axtar/14-digits-nixie-calculator/Docs/!_Start here.pdf

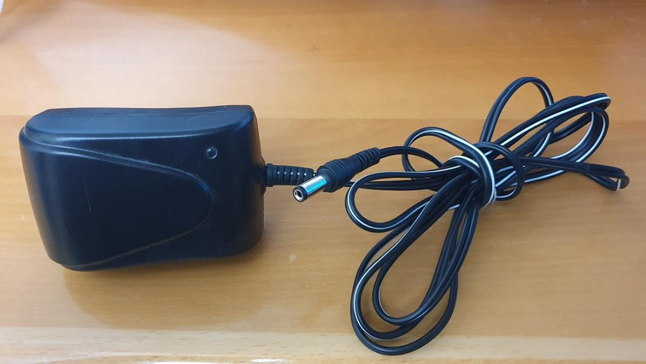
[picture p9: figure]
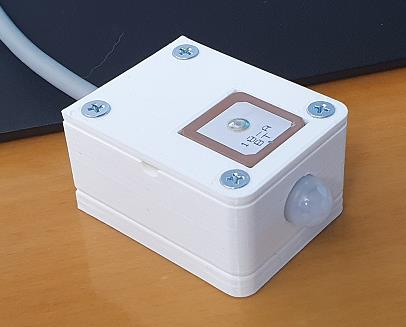
[picture p10: figure]
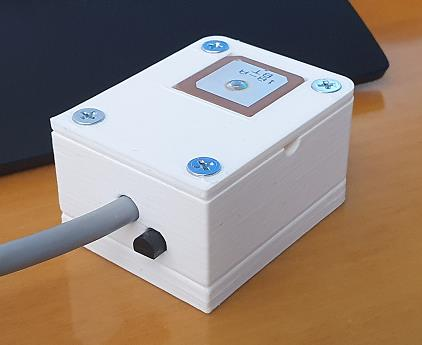
[picture p11: figure]

June 16, 2021 | Start here – Version 0.1 | Page 1 of 1

## Start here

### WARNING: nixies need high voltage to light up. If you choose to build the

calculator, you are doing so at your own risk.

Please read all the documents in Docs first.

### BOM/Components

I have tried to use available and modern components but currently some of the IC’s have long lead times. That seems to be a common problem these days.

### Power supply

The calculator needs a stabilized 12V DC 2A center positive power supply.

### Optional peripherals

You can connect a GPS module with U-Blox chip, a PIR and a DS18B20+ temperature sensor. All the peripherals must work with 5V input voltage and 3.3V logic. The pictures show the all-in-one solution I designed for this project.
