axtar/14-digits-nixie-calculator/Docs/Importing PCB project files.pdf

June 10, 2021 | Draft – Version 0.1 | Page 1 of 1

## Importing PCB project files

I will not provide the Gerber files, but you can import the project files into EasyEDA. This way, you can check the design and modify the boards according to your needs. You generate your own Gerber files, and it is up to you to make sure that they are correct.

To import the projects, try this or follow the instructions on EasyEDA:

- Unzip the project file, you will get a schematic and a pcb file (json format)

Go to EasyEDA Designer (you need an account)

- Import schematic

->File->Open->EasyEDA

Select schematic file

->Open

- Save schematic:

->File->Save As

Select -Save as New Project-

Enter -Title- (a different name for every project you want to import)

->Save

- Import PCB:

->File->Open->EasyEDA

Select PCB file

->Open

- Save pcb:

->File->Save As

Select -Save to Existing Project-

Enter -Title- (board name)

Set the -Project Owner- to yourself

Select -Project- (the project you created before)

->Save

The label board has no schematic, you can import just the PCB file and save it as new project.
