axtar/14-digits-nixie-calculator/Docs/Keyboard layout.pdf

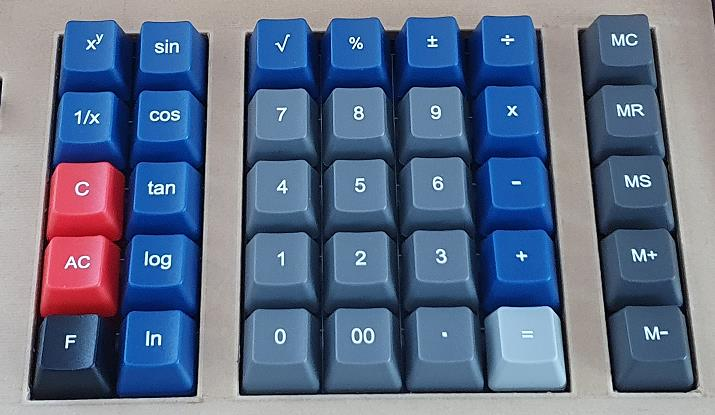
[picture p12: figure]

June 11, 2021 | Draft - Version 0.1 | Page 1 of 2

## Keyboard layout

For this project we need some custom Cherry MX keycaps. The picture shows the keyboard layout and the keycap type (Row1 – Row4). All keycaps are 1x1.

R4 →
R3 →
R2 →
R1 →
R1 →

Classic

You can order some blank keycaps and print your own legends, for example using sublimation ink, sublimation paper and an inkjet printer. You can also order custom keycaps from a service provider.

I’ve used Inkscape to modify the 104-key template file (V6.0) provided by WASD Keyboards. I cannot provide the template file but in the svg file you can see the legends layer I have designed for my keyboard.

If you decide to use my design as a starting point, you can try this:

- Download the 104-key template file for Inkscape from the support area
- Open the template with Inkscape and hide the “message” layer
- Add a new layer called “Nixie Calculator” and make sure it’s selected, visible and unlocked
- Open another instance of Inkscape
- Open the “Keycaps/Nixie_Calculator_extended.svg” file
- Select all legends (ctrl-a). Make a note of the X and Y coordinates of the selection
- Copy the legends (ctrl-c)
- Go to the instance with the template file
- Paste the legends (ctrl-v)
- Bring the legends into position by setting the X and Y coordinates to the previously noted values. Now you can modify the legends as you wish. Check that everything is correctly aligned.
- Important: set the desired legend colors. If you want white legends as shown in the picture, you must set the text color to white.
- Unhide the “message” layer and carefully read and follow the instructions shown in the template before placing your order.

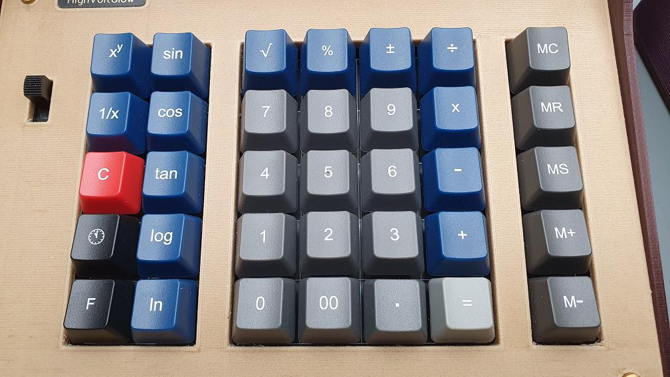
[picture p13: figure]

June 11, 2021 | Draft - Version 0.1 | Page 2 of 2

I can think of two options:

- Classic mode:
F | -> clock mode and settings
AC | -> all clear
C | -> clear last
- Alternate mode:
F -> shift (second level of functions)
- -> clock mode and settings
C -> all clear

Alternate

If you want to use the alternate mode, it is also possible to add a second level of functions to the keycap legends. For example, something like this:
