axtar/14-digits-nixie-calculator/PCB/Pictures/Boards 2D/Nixie Calculator Extended Keyboard Bottom 2D.jpg

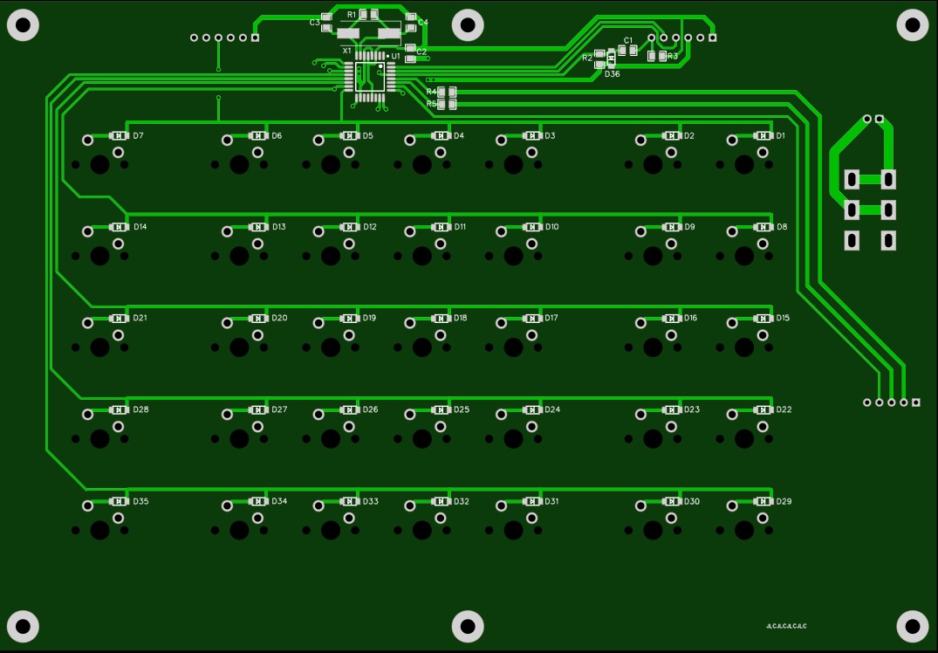
PCB/Pictures/Boards 2D/Nixie Calculator Extended Keyboard Bottom 2D.jpg
