axtar/14-digits-nixie-calculator/PCB/Pictures/Boards 2D/Nixie Calculator IN-16 Display With Sockets Bottom 2D.jpg

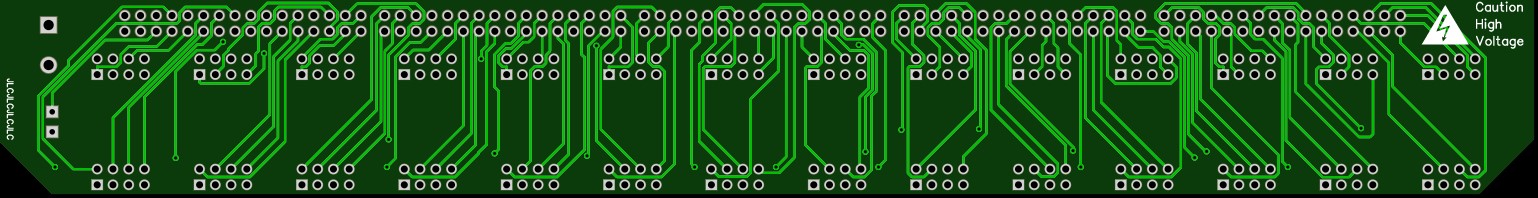
PCB/Pictures/Boards 2D/Nixie Calculator IN-16 Display With Sockets Bottom 2D.jpg
