axtar/14-digits-nixie-calculator/PCB/Pictures/Boards 2D/Nixie Calculator IN-16 Driver Top 2D.jpg

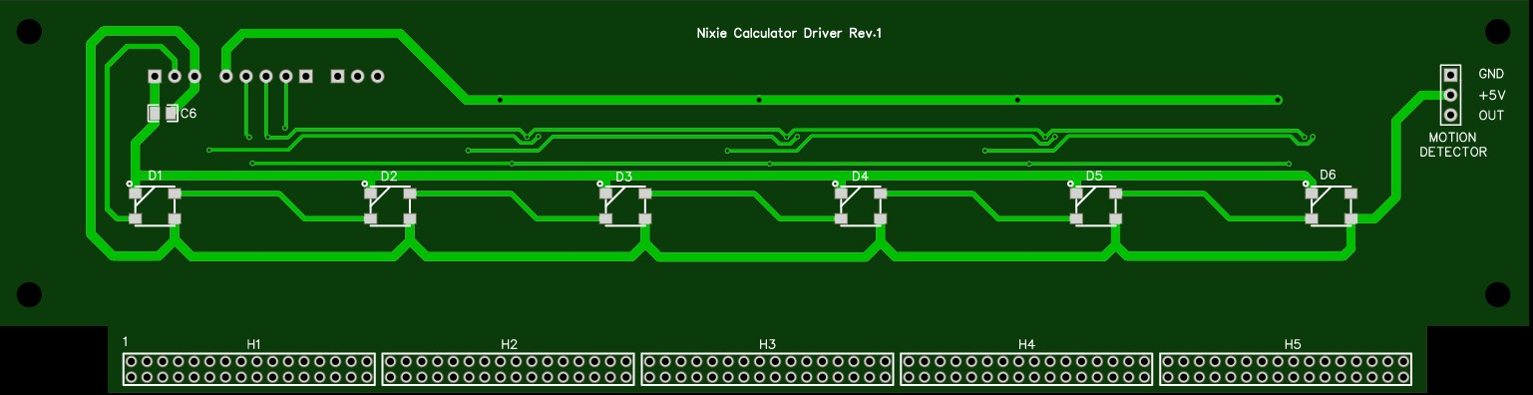
PCB/Pictures/Boards 2D/Nixie Calculator IN-16 Driver Top 2D.jpg
