axtar/14-digits-nixie-calculator/PCB/Pictures/Boards 2D/Nixie Calculator IN-17 Display & Driver With Sockets Top 2D.jpg

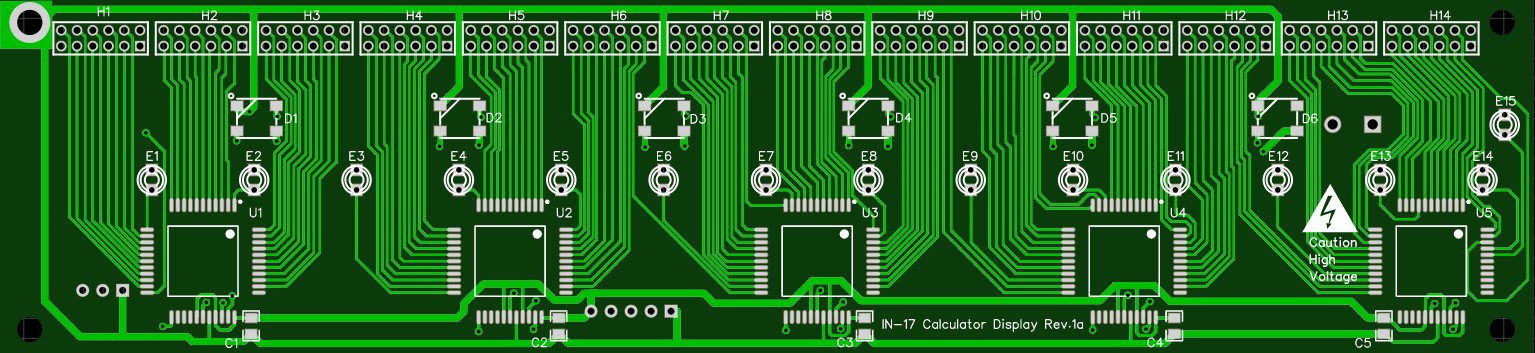
PCB/Pictures/Boards 2D/Nixie Calculator IN-17 Display & Driver With Sockets Top 2D.jpg
