axtar/14-digits-nixie-calculator/PCB/Pictures/Boards 2D/Nixie Calculator IN-17 Socket Top 2D.jpg

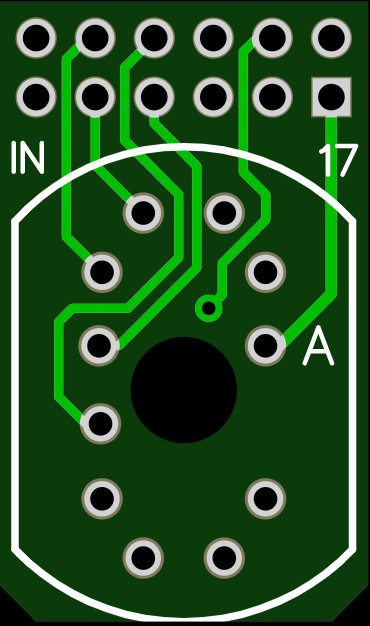
PCB/Pictures/Boards 2D/Nixie Calculator IN-17 Socket Top 2D.jpg
