axtar/14-digits-nixie-calculator/PCB/Pictures/Boards 3D/Nixie  Calculator Controller Top 3D.jpg

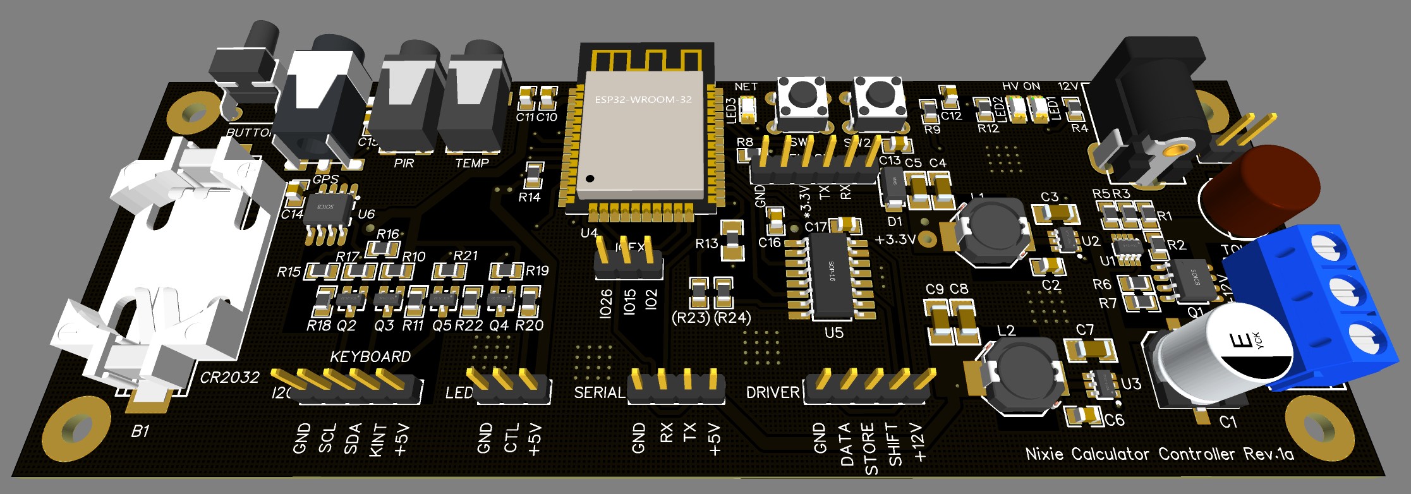
PCB/Pictures/Boards 3D/Nixie Calculator Controller Top 3D.jpg
