axtar/14-digits-nixie-calculator/PCB/Pictures/Boards 3D/Nixie Calculator Extended Keyboard Top  3D.jpg

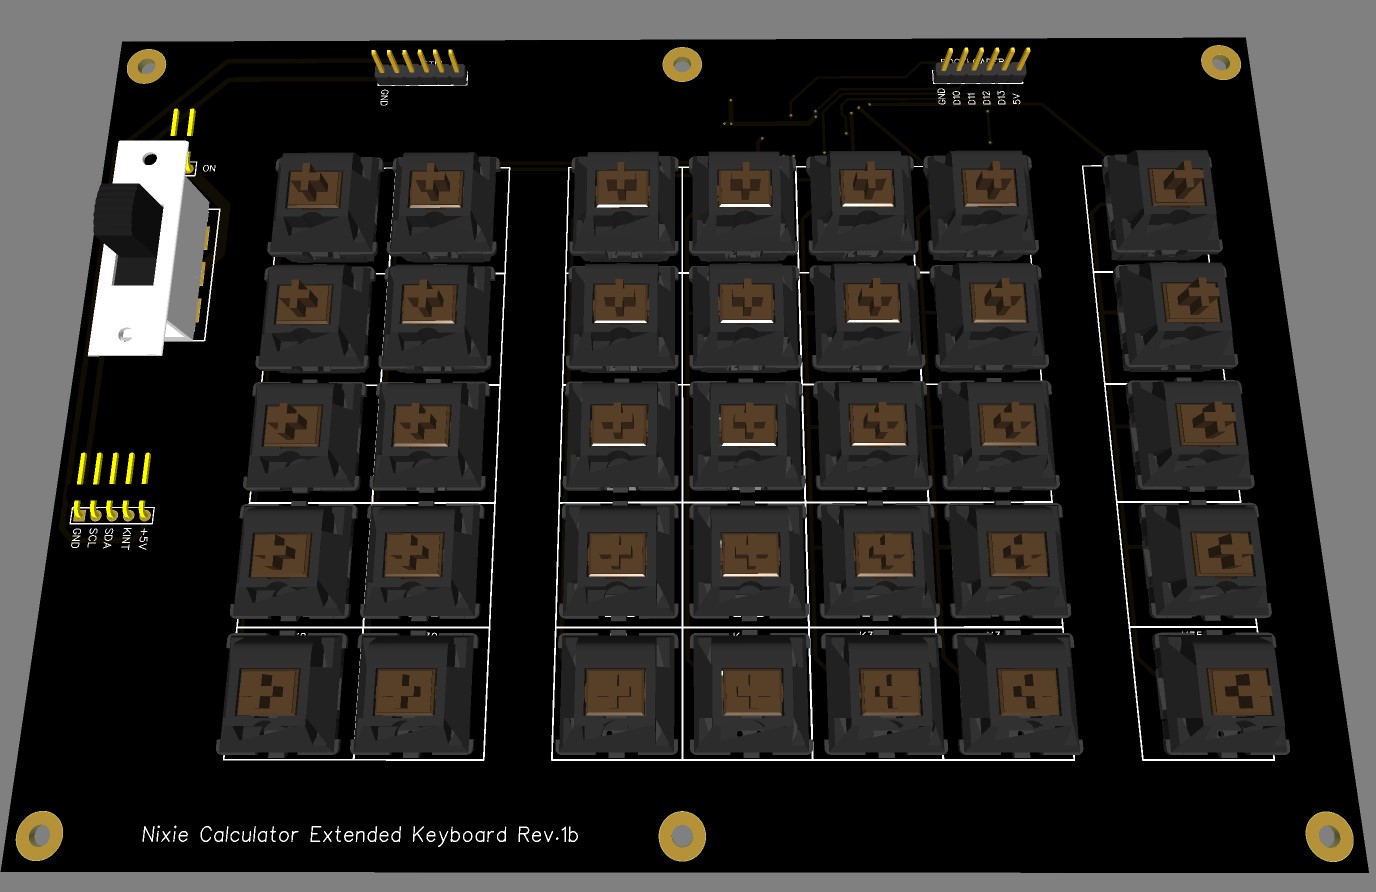
PCB/Pictures/Boards 3D/Nixie Calculator Extended Keyboard Top 3D.jpg
