axtar/14-digits-nixie-calculator/PCB/Pictures/Boards 3D/Nixie Calculator High Voltage PSU Top 3D.jpg

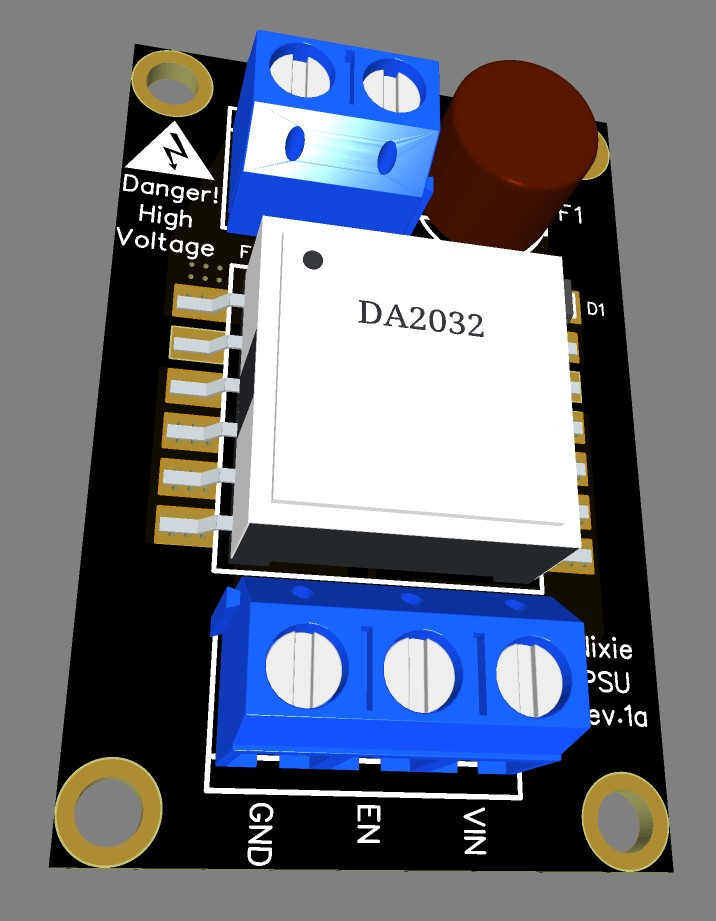
PCB/Pictures/Boards 3D/Nixie Calculator High Voltage PSU Top 3D.jpg
