axtar/14-digits-nixie-calculator/PCB/Pictures/Boards 3D/Nixie Calculator IN-16 Driver Top 3D.jpg

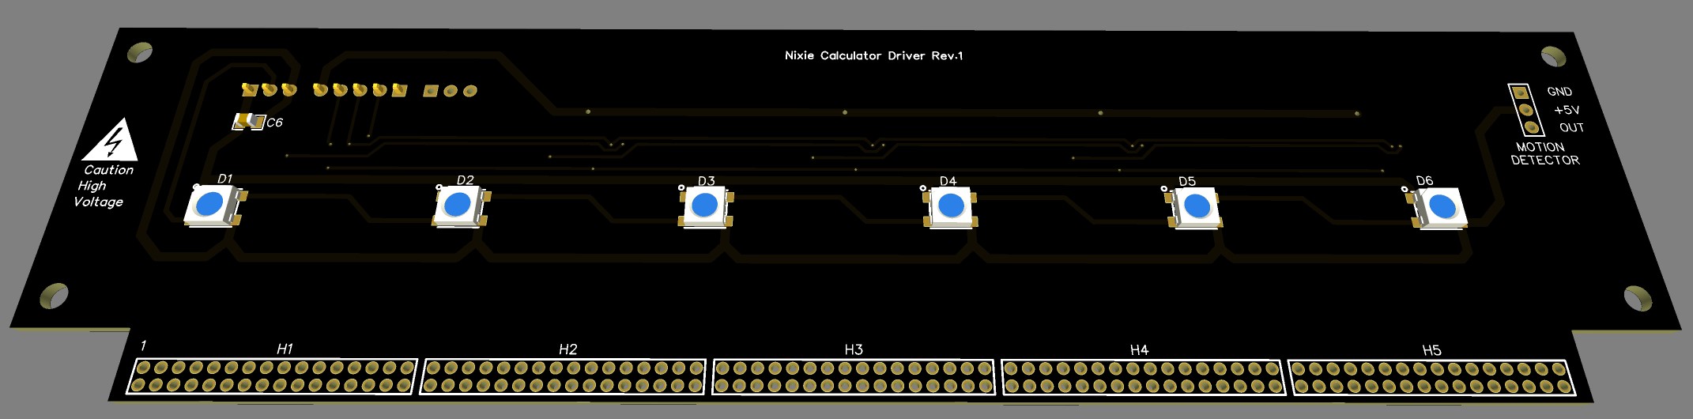
PCB/Pictures/Boards 3D/Nixie Calculator IN-16 Driver Top 3D.jpg
