axtar/14-digits-nixie-calculator/PCB/Pictures/Boards 3D/Nixie Calculator IN-16 Socket 3D.jpg

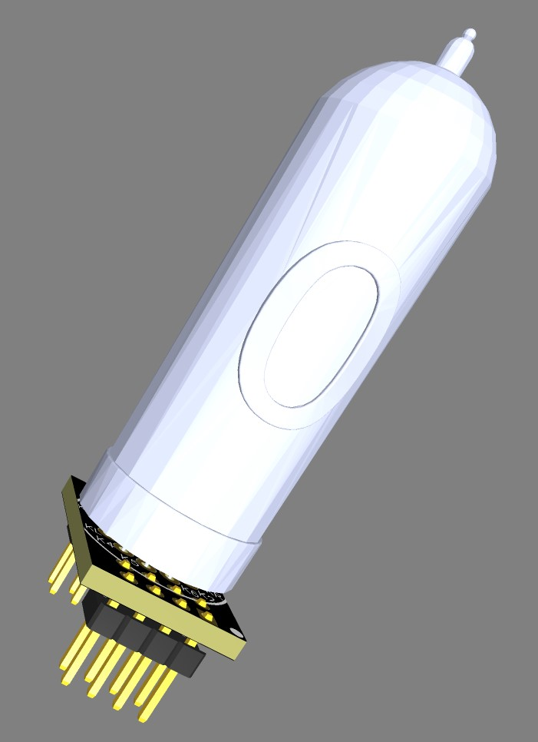
PCB/Pictures/Boards 3D/Nixie Calculator IN-16 Socket 3D.jpg
