axtar/14-digits-nixie-calculator/PCB/Pictures/Boards 3D/Nixie Calculator IN-17 Display & Driver With Sockets Top 3D.jpg

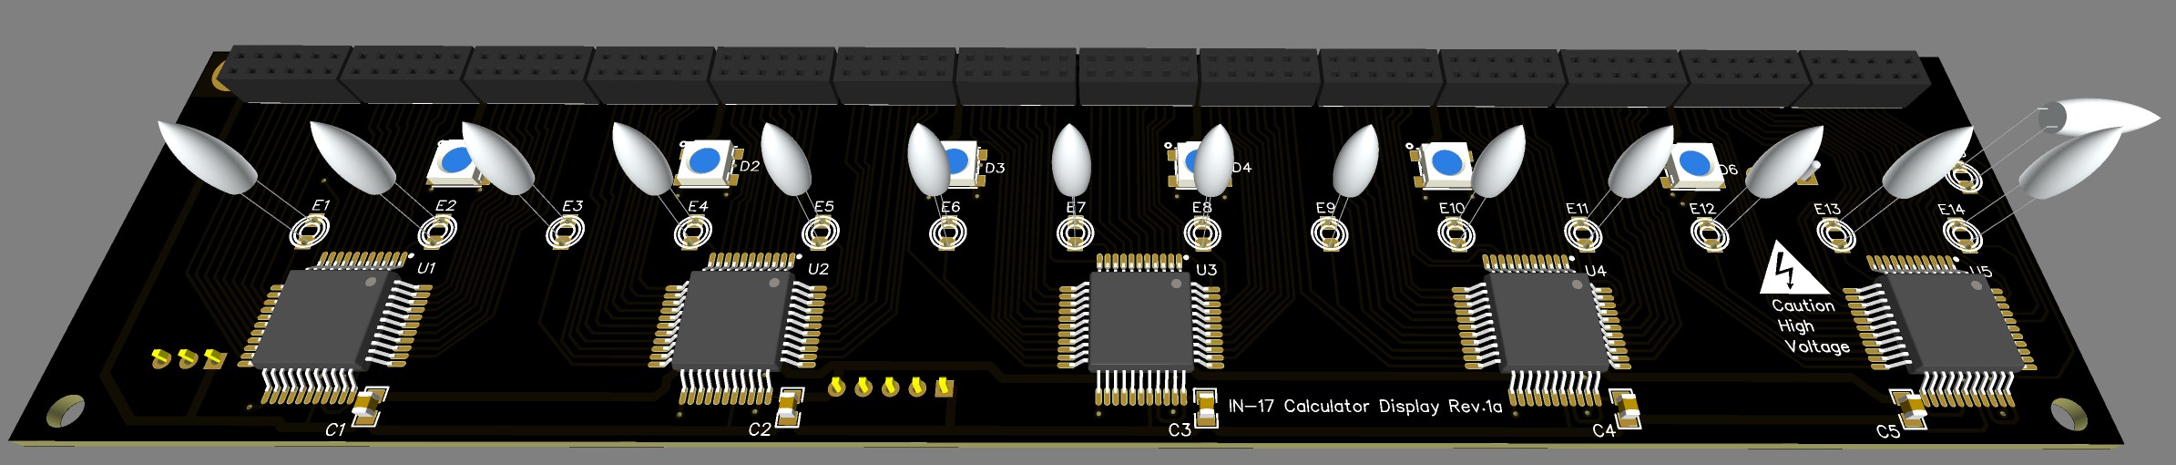
PCB/Pictures/Boards 3D/Nixie Calculator IN-17 Display & Driver With Sockets Top 3D.jpg
