axtar/14-digits-nixie-calculator/PCB/Pictures/Boards 3D/Nixie Calculator IN-17 Socket.jpg

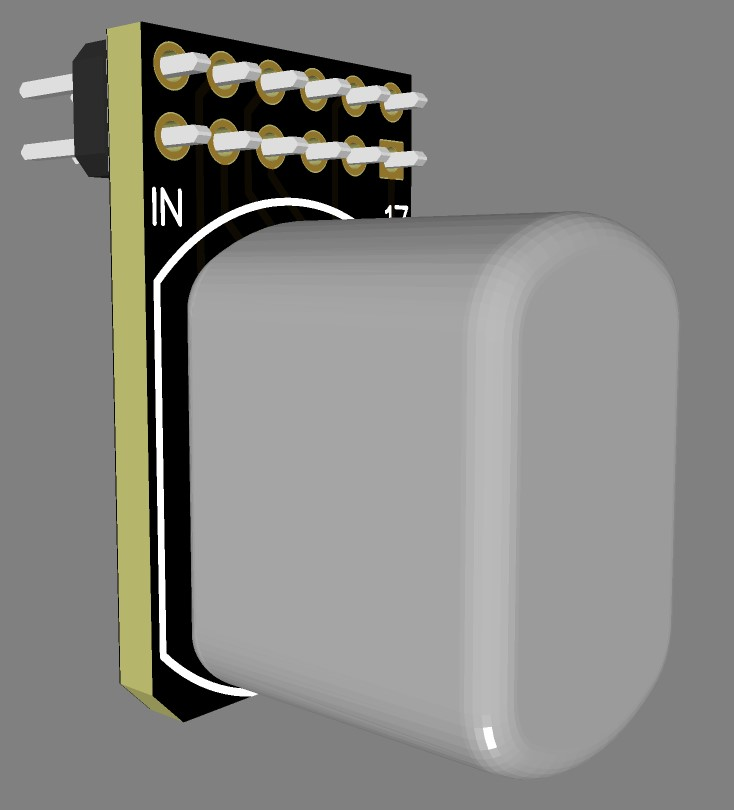
PCB/Pictures/Boards 3D/Nixie Calculator IN-17 Socket.jpg
