axtar/14-digits-nixie-calculator/Schematics/Schematic_Nixie Calculator IN-16 Display With Sockets.pdf

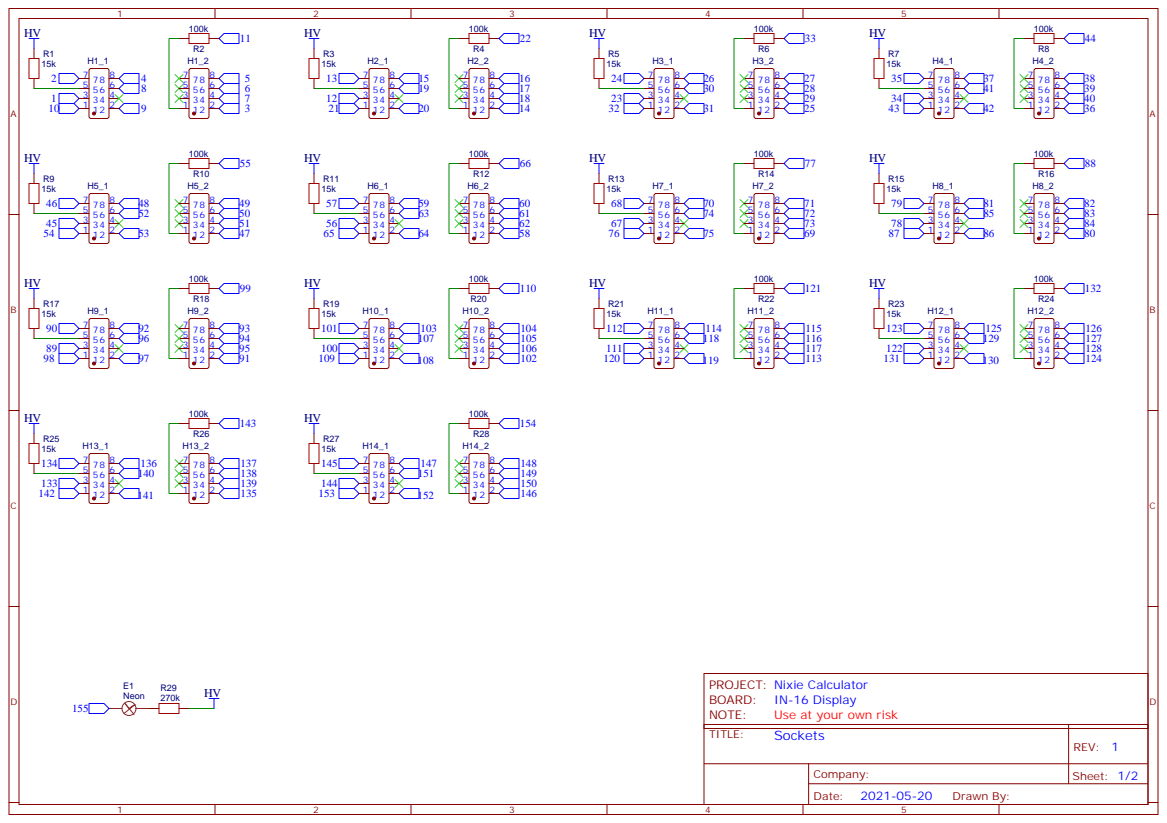
[picture p81: page 1]

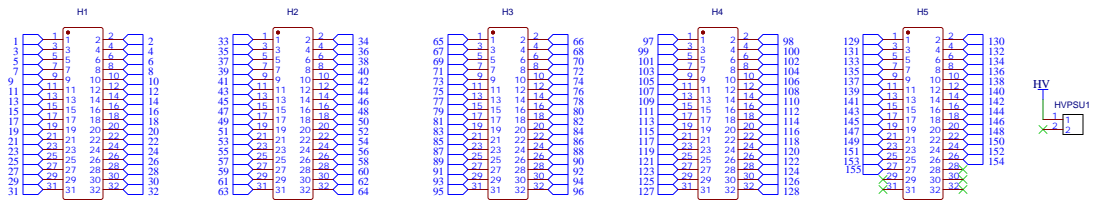
[picture p82: page 2]
