axtar/14-digits-nixie-calculator/Schematics/Schematic_Nixie Calculator IN-16 Driver.pdf

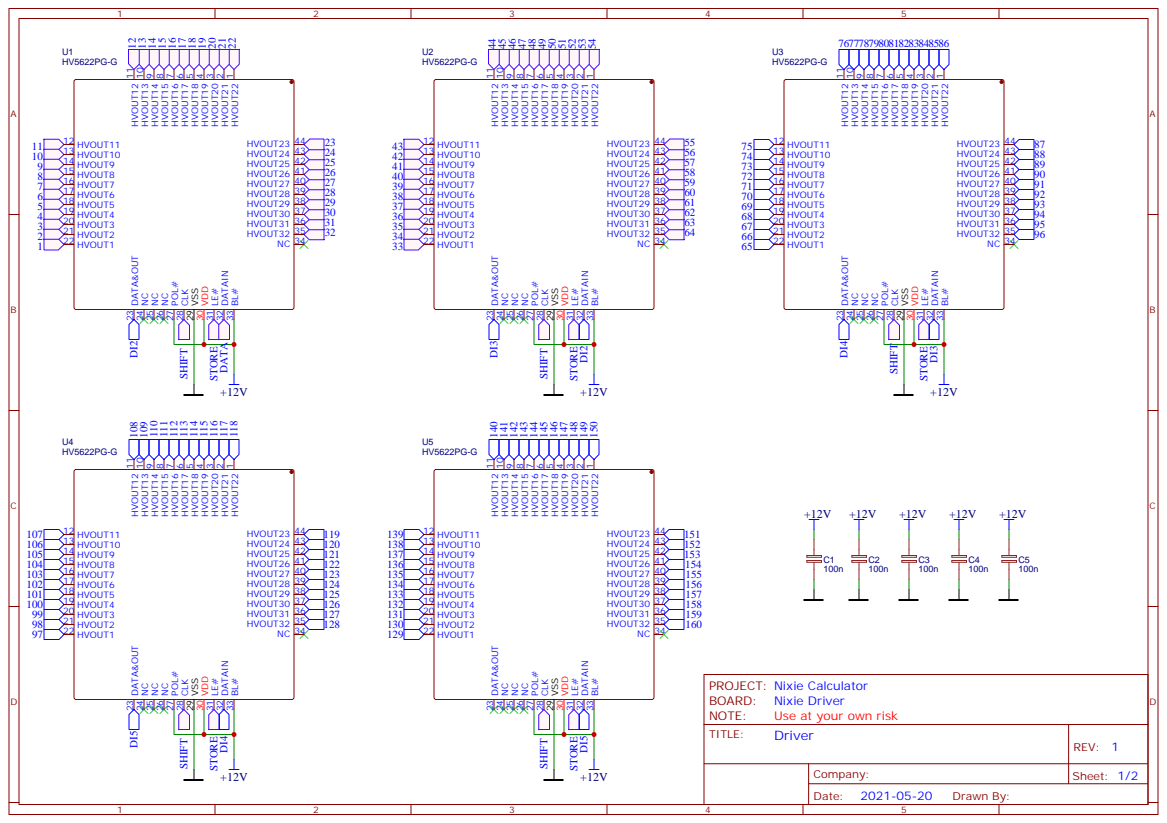
[picture p83: page 1]

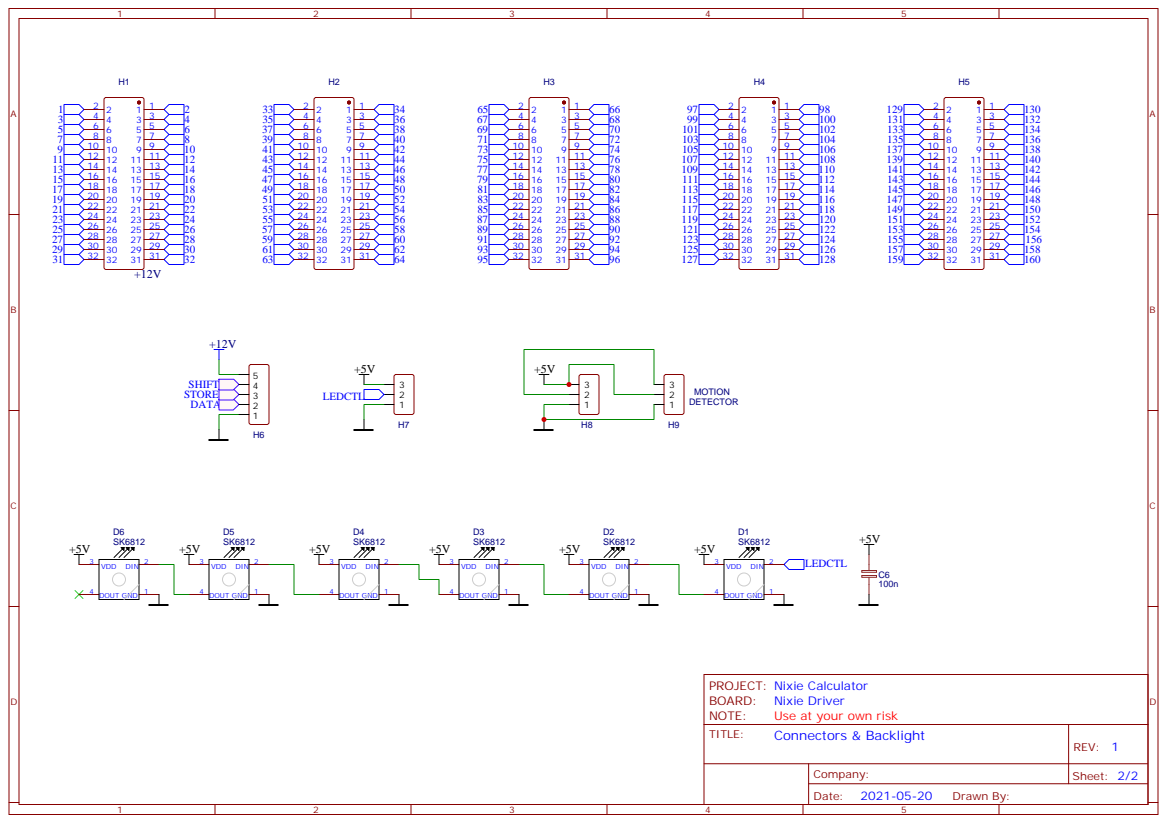
[picture p84: page 2]
