axtar/14-digits-nixie-calculator/Schematics/Schematic_Nixie Calculator IN-16 Socket.pdf

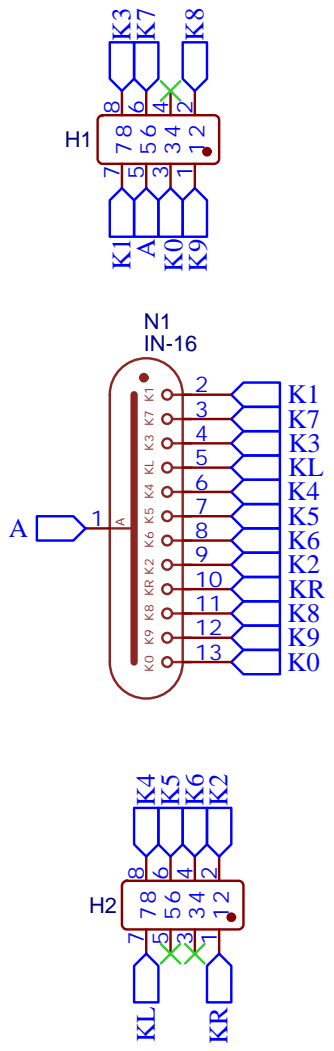
[picture p85: page 1]
