axtar/14-digits-nixie-calculator/Schematics/Schematic_Nixie Calculator IN-17 Display & Driver with Sockets.pdf

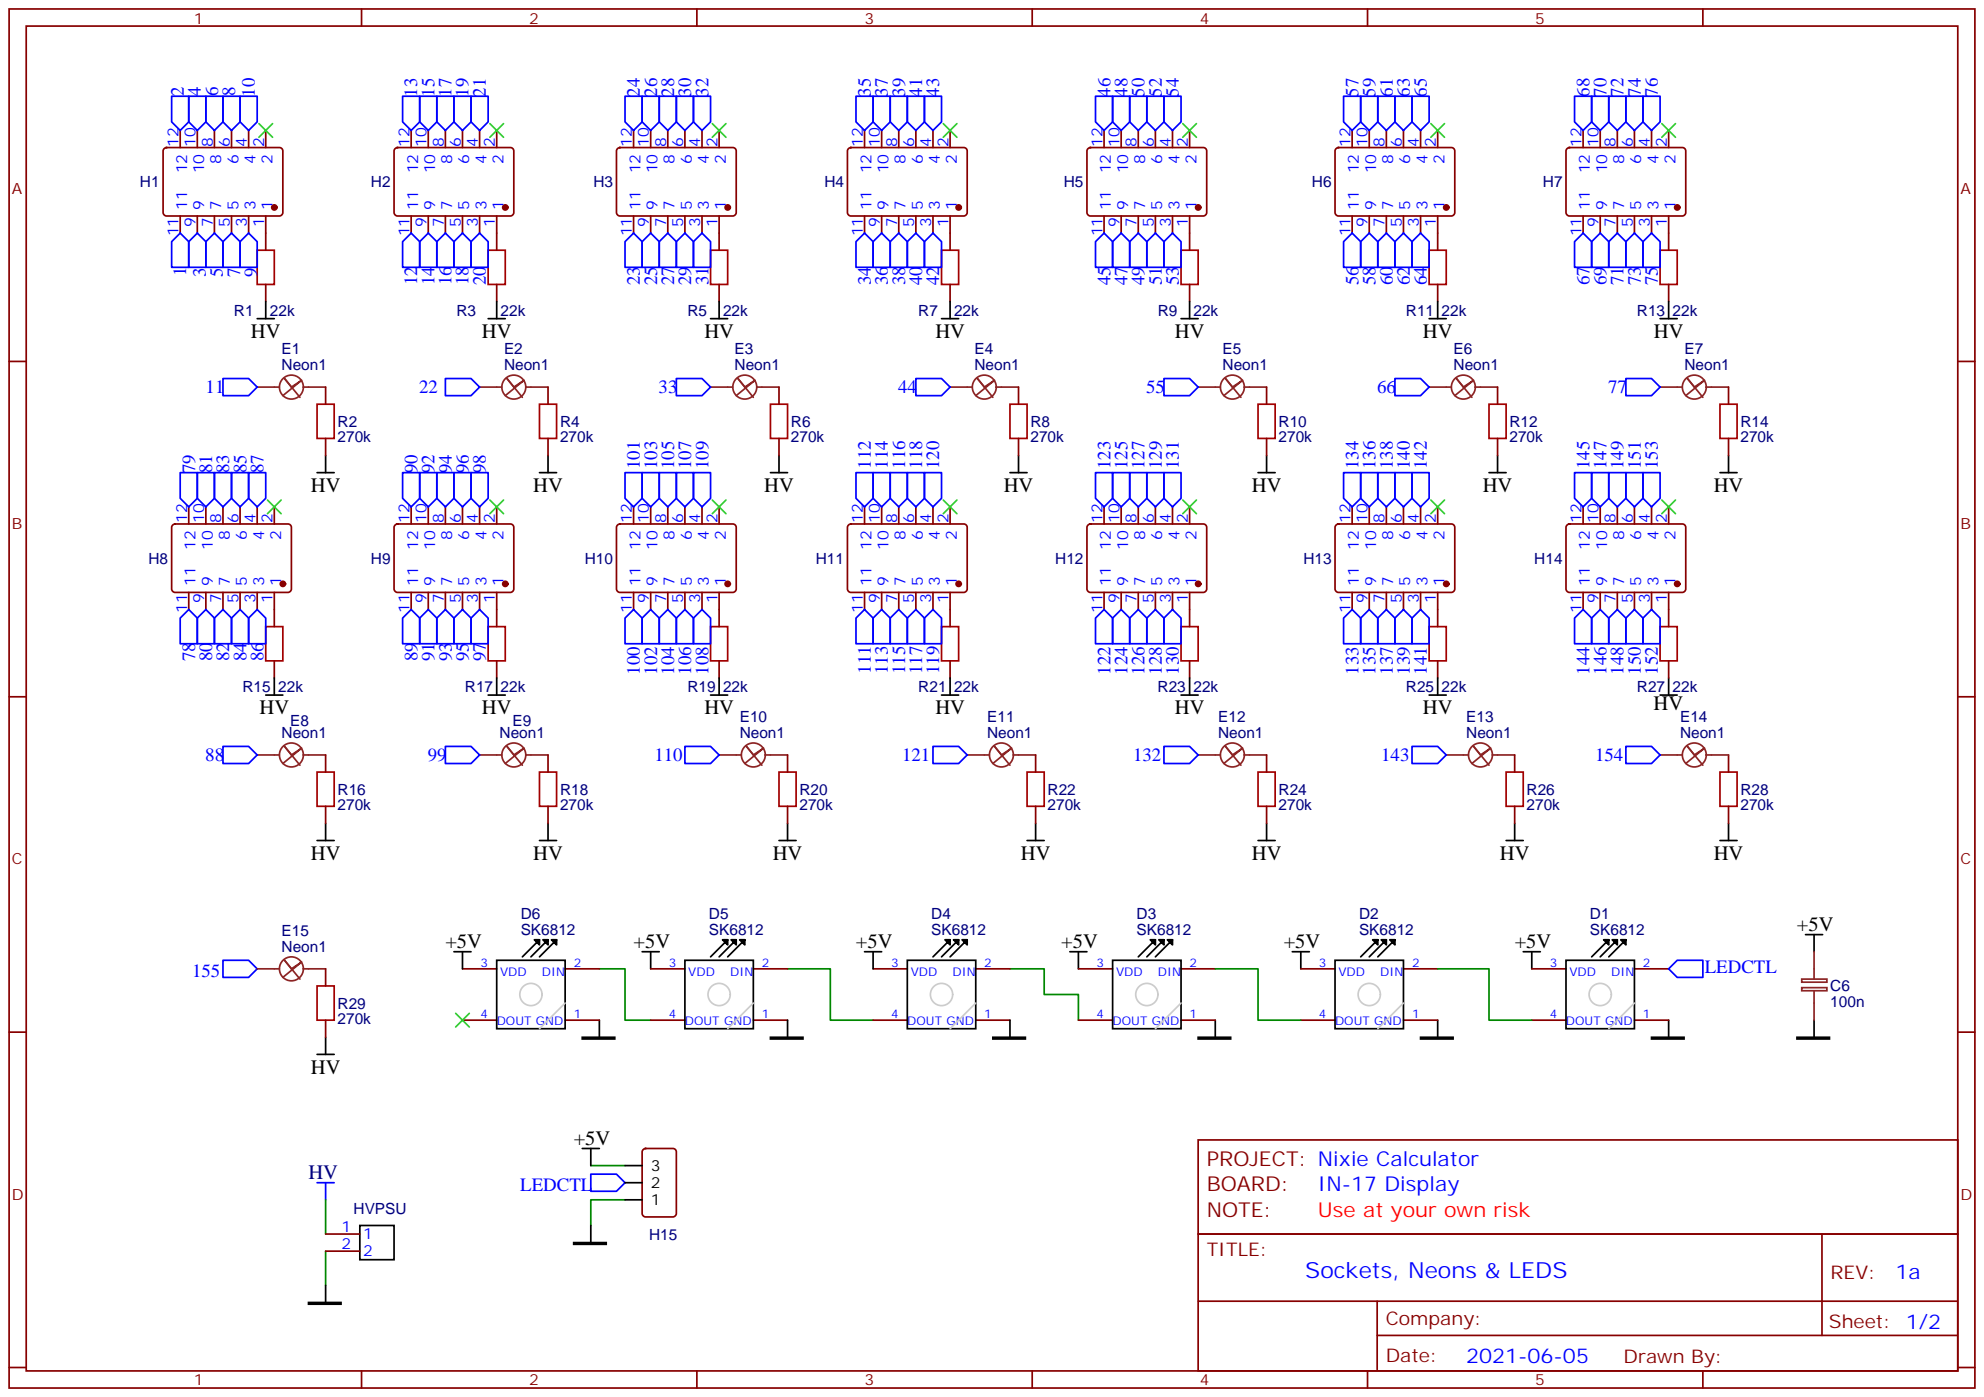
[picture p86: page 1]

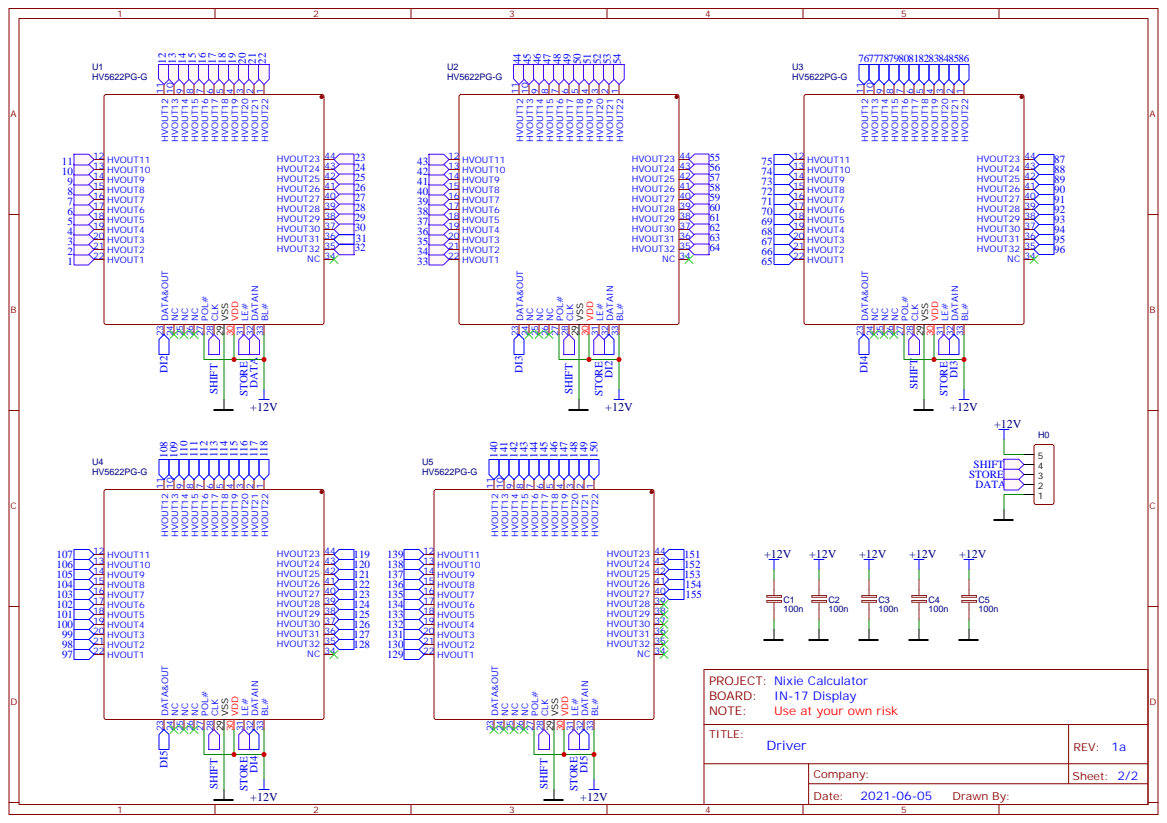
[picture p87: page 2]
