axtar/14-digits-nixie-calculator/Schematics/Schematic_Nixie Calculator IN-17 Socket.pdf

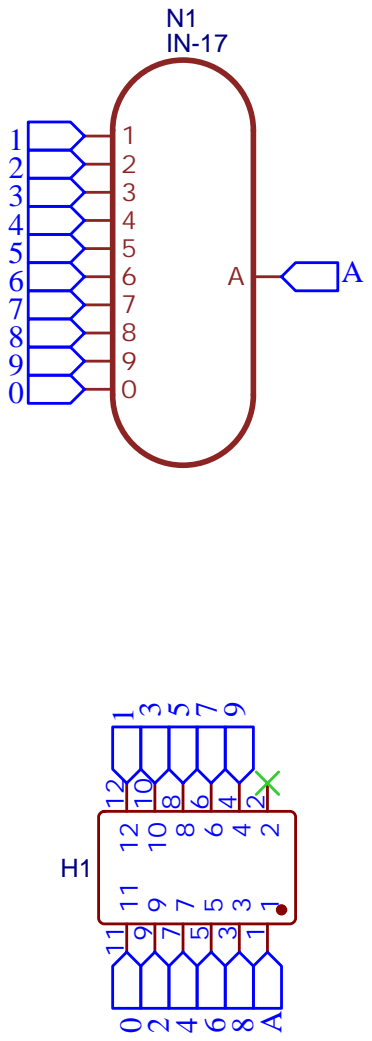
[picture p88: page 1]
